ISF-H-BRS/ReDeX/Images/HubBack.jpg

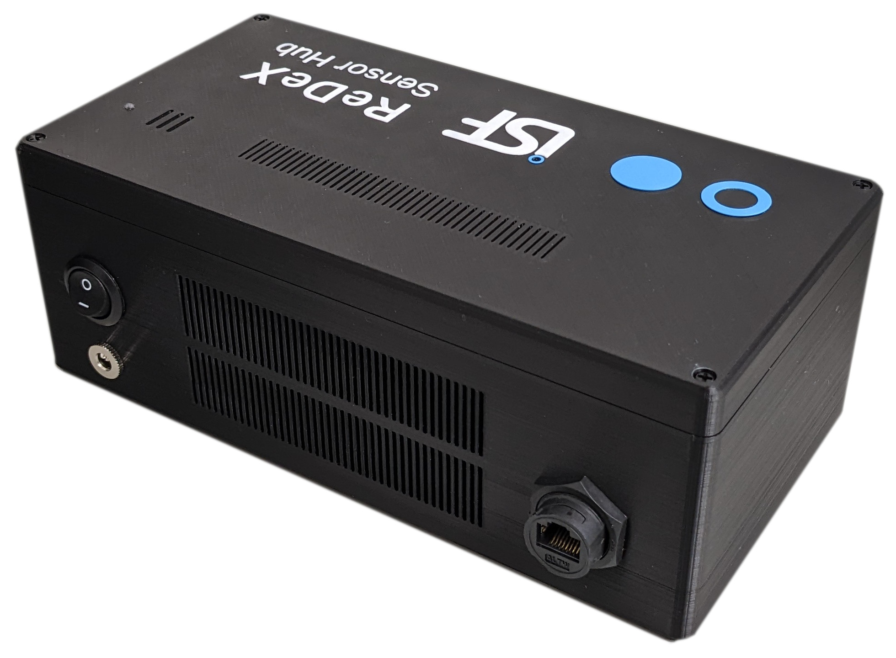
Images/HubBack.jpg
