ISF-H-BRS/ReDeX/Images/SensorViewer.png

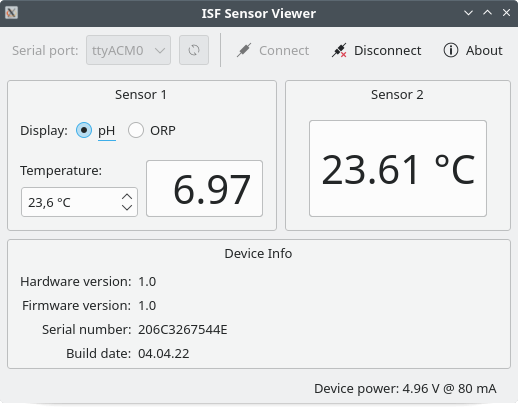
Images/SensorViewer.png
