ISF-H-BRS/ReDeX/Firmware/ConductanceMaster/Core/Inc/main.h

#define BUS_VOLTAGE_Pin GPIO_PIN_0
#define BUS_VOLTAGE_GPIO_Port GPIOA
#define BUS_CURRENT_Pin GPIO_PIN_1
#define BUS_CURRENT_GPIO_Port GPIOA
#define SLAVE2_CS_Pin GPIO_PIN_4
#define SLAVE2_CS_GPIO_Port GPIOA
#define SLAVE2_SCK_Pin GPIO_PIN_5
#define SLAVE2_SCK_GPIO_Port GPIOA
#define SLAVE2_MISO_Pin GPIO_PIN_6
#define SLAVE2_MISO_GPIO_Port GPIOA
#define SLAVE2_MOSI_Pin GPIO_PIN_7
#define SLAVE2_MOSI_GPIO_Port GPIOA
#define SLAVE2_CON_Pin GPIO_PIN_4
#define SLAVE2_CON_GPIO_Port GPIOC
#define SLAVE2_DRDY_Pin GPIO_PIN_5
#define SLAVE2_DRDY_GPIO_Port GPIOC
#define SLAVE1_CS_Pin GPIO_PIN_12
#define SLAVE1_CS_GPIO_Port GPIOB
#define SLAVE1_SCK_Pin GPIO_PIN_13
#define SLAVE1_SCK_GPIO_Port GPIOB
#define SLAVE1_MISO_Pin GPIO_PIN_14
#define SLAVE1_MISO_GPIO_Port GPIOB
#define SLAVE1_MOSI_Pin GPIO_PIN_15
#define SLAVE1_MOSI_GPIO_Port GPIOB
#define SLAVE1_CON_Pin GPIO_PIN_6
#define SLAVE1_CON_GPIO_Port GPIOC
#define SLAVE1_DRDY_Pin GPIO_PIN_7
#define SLAVE1_DRDY_GPIO_Port GPIOC
#define VARIANT1_Pin GPIO_PIN_11
#define VARIANT1_GPIO_Port GPIOC
#define VARIANT0_Pin GPIO_PIN_12
#define VARIANT0_GPIO_Port GPIOC
#define STATUS_BAD_Pin GPIO_PIN_3
#define STATUS_BAD_GPIO_Port GPIOB
#define STATUS_GOOD_Pin GPIO_PIN_4
#define STATUS_GOOD_GPIO_Port GPIOB
