ISF-H-BRS/ReDeX/Firmware/SensorBoard/Core/Src/User/sensormanager.cpp

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
#include "assert.h"
#include "config.h"
#include "sensormanager.h"

// ---------------------------------------------------------------------------------------------- //

SensorManager::SensorManager()
{
    static constexpr std::array<I2C_HandleTypeDef*, SensorCount> SensorHandles = {
        Config::Sensor1Handle, Config::Sensor2Handle
    };

    for (size_t i = 0; i < SensorCount; ++i)
    {
        ASSERT(m_sensors[i] == nullptr);

        char* buffer = m_memPool.getNextFreeBuffer();
        I2C_HandleTypeDef* handle = SensorHandles[i];

        const Sensor::Type type = readSensorType(i);

        switch (type)
        {
        case Sensor::Type::pH_ORP:
            m_sensors[i] = new (buffer) PhSensor(handle);
            break;

        case Sensor::Type::Temperature:
            m_sensors[i] = new (buffer) TemperatureSensor(handle);
            break;

        default:
            m_sensors[i] = new (buffer) NoneSensor();
            break;
        }
    }
}

// ---------------------------------------------------------------------------------------------- //

SensorManager::~SensorManager()
{
    for (auto& sensor : m_sensors)
    {
        if (sensor)
            sensor->~Sensor();

        sensor = nullptr;
    }
}

// ---------------------------------------------------------------------------------------------- //

auto SensorManager::sensorType(uint8_t sensor) const -> Sensor::Type
{
    ASSERT(sensor < SensorCount);
    return m_sensors[sensor]->type();
}

// ---------------------------------------------------------------------------------------------- //

auto SensorManager::sensorValue(uint8_t sensor) const -> double
{
    ASSERT(sensor < SensorCount);
    return m_sensors[sensor]->value();
}

// ---------------------------------------------------------------------------------------------- //

void SensorManager::update()
{
    for (auto sensor : m_sensors)
        sensor->update();
}

// ---------------------------------------------------------------------------------------------- //

auto SensorManager::readSensorType(uint8_t sensor) const -> Sensor::Type
{
    ASSERT(sensor < SensorCount);

    struct Input
    {
        GPIO_TypeDef* port;
        uint32_t pin;
    };

    static constexpr std::array<std::array<Input, 2>, SensorCount> Inputs = {{
        {{{ ID1_0_GPIO_Port, ID1_0_Pin }, { ID1_1_GPIO_Port, ID1_1_Pin }}},
        {{{ ID2_0_GPIO_Port, ID2_0_Pin }, { ID2_1_GPIO_Port, ID2_1_Pin }}}
    }};

    const Input& input0 = Inputs[sensor][0];
    const Input& input1 = Inputs[sensor][1];

    const GPIO_PinState state0 = HAL_GPIO_ReadPin(input0.port, input0.pin);
    const GPIO_PinState state1 = HAL_GPIO_ReadPin(input1.port, input1.pin);

    const unsigned int type = ((state1 == GPIO_PIN_SET ? 1 : 0) << 1) |
                              ((state0 == GPIO_PIN_SET ? 1 : 0) << 0);

    return static_cast<Sensor::Type>(type);
}

// ---------------------------------------------------------------------------------------------- //
