ISF-H-BRS/ReDeX/Firmware/Potentiostat/Core/Inc/main.h

#define PWR_ENABLE_Pin GPIO_PIN_14
#define PWR_ENABLE_GPIO_Port GPIOC
#define ADC_CONVST_Pin GPIO_PIN_2
#define ADC_CONVST_GPIO_Port GPIOA
#define ADC_CS1_Pin GPIO_PIN_3
#define ADC_CS1_GPIO_Port GPIOA
#define ADC_CS2_Pin GPIO_PIN_4
#define ADC_CS2_GPIO_Port GPIOA
#define ADC_SCK_Pin GPIO_PIN_5
#define ADC_SCK_GPIO_Port GPIOA
#define ADC_MISO_Pin GPIO_PIN_6
#define ADC_MISO_GPIO_Port GPIOA
#define DAC_AUX_Pin GPIO_PIN_7
#define DAC_AUX_GPIO_Port GPIOA
#define STATUS_GOOD_Pin GPIO_PIN_0
#define STATUS_GOOD_GPIO_Port GPIOB
#define STATUS_BAD_Pin GPIO_PIN_1
#define STATUS_BAD_GPIO_Port GPIOB
#define OUTPUT_ENABLE_Pin GPIO_PIN_8
#define OUTPUT_ENABLE_GPIO_Port GPIOA
#define MUX_A0_Pin GPIO_PIN_3
#define MUX_A0_GPIO_Port GPIOB
#define MUX_A1_Pin GPIO_PIN_4
#define MUX_A1_GPIO_Port GPIOB
#define MUX_EN_Pin GPIO_PIN_5
#define MUX_EN_GPIO_Port GPIOB
#define SCL_Pin GPIO_PIN_6
#define SCL_GPIO_Port GPIOB
#define SDA_Pin GPIO_PIN_7
#define SDA_GPIO_Port GPIOB
