ISF-H-BRS/ReDeX/Firmware/ConductanceSlave/Core/Src/User/signalgenerator.cpp

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
#include "signalgenerator.h"
#include "wavegenerator.h"

#include <algorithm> // for clamp()

// ---------------------------------------------------------------------------------------------- //

namespace {
    constexpr uint32_t DacZeroChannel   = DAC_CHANNEL_1;
    constexpr uint32_t DacSignalChannel = DAC_CHANNEL_2;
    constexpr uint32_t DacDcOffset      = 2047;
    constexpr uint32_t DacMaximumValue  = 4095;
}

// ---------------------------------------------------------------------------------------------- //

SignalGenerator::SignalGenerator()
{
    HAL_DAC_Start(m_dacHandle, DacZeroChannel);
    HAL_DAC_Start(m_dacHandle, DacSignalChannel);

    setValue(DacZeroChannel, DacDcOffset);
    setValue(DacSignalChannel, DacDcOffset);
}

// ---------------------------------------------------------------------------------------------- //

SignalGenerator::~SignalGenerator()
{
    HAL_DAC_Stop(m_dacHandle, DacZeroChannel);
    HAL_DAC_Stop(m_dacHandle, DacSignalChannel);
}

// ---------------------------------------------------------------------------------------------- //

void SignalGenerator::reset()
{
    m_waveform = Waveform::None;
    m_frequency = 1.0;
    m_amplitude = 0.0;

    m_signalPosition = 0;

    setValue(DacSignalChannel, DacDcOffset);
}

// ---------------------------------------------------------------------------------------------- //

void SignalGenerator::setup(Waveform waveform, unsigned int frequency, Real amplitude)
{
    frequency = std::clamp(frequency, MinimumFrequency, MaximumFrequency);
    amplitude = std::clamp(amplitude, MinimumAmplitude, MaximumAmplitude);

    m_waveform = waveform;
    m_frequency = static_cast<Real>(frequency);
    m_amplitude = 0.5 / MaximumAmplitude * amplitude;
}

// ---------------------------------------------------------------------------------------------- //

void SignalGenerator::update()
{
    using WaveGenerator = WaveGenerator<Real>;

    static constexpr auto DcOffset = static_cast<Real>(0.5);
    static constexpr auto One = static_cast<Real>(1.0);
    static constexpr auto Zero = static_cast<Real>(0.0);

    const Real time = m_signalPosition * (One / SampleRate);

    if (++m_signalPosition >= SampleRate)
        m_signalPosition = 0;

    Real signal = DcOffset;

    if (m_waveform == Waveform::Sine)
        signal = WaveGenerator::qsine(time, m_frequency, m_amplitude, DcOffset);
    else if (m_waveform == Waveform::Square)
        signal = WaveGenerator::square(time, m_frequency, m_amplitude, DcOffset);
    else if (m_waveform == Waveform::Triangle)
        signal = WaveGenerator::triangle(time, m_frequency, m_amplitude, DcOffset);
    else if (m_waveform == Waveform::Sawtooth)
        signal = WaveGenerator::sawtooth(time, m_frequency, m_amplitude, DcOffset);

    signal = std::clamp(signal, Zero, One);

    const uint16_t outValue = static_cast<uint16_t>(DacMaximumValue * signal);
    setValue(DacSignalChannel, outValue);
}

// ---------------------------------------------------------------------------------------------- //

void SignalGenerator::setValue(uint32_t channel, uint32_t value)
{
    HAL_DAC_SetValue(m_dacHandle, channel, DAC_ALIGN_12B_R, value);
}

// ---------------------------------------------------------------------------------------------- //
