ISF-H-BRS/ReDeX/Firmware/Potentiostat/Core/Inc/User/ltc2945.h

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
#pragma once

#include <cstdint>
#include <span>

class Ltc2945
{
public:
    enum class Address : uint8_t
    {
        A0 = 0xce,
        A1 = 0xd0,
        A2 = 0xd2,
        A3 = 0xd4,
        A4 = 0xd6,
        A5 = 0xd8,
        A6 = 0xda,
        A7 = 0xdc,
        A8 = 0xde
    };

    static constexpr uint8_t AddressCount = 9;

    class Interface
    {
        friend class Ltc2945;

        virtual void write(uint8_t address, uint8_t reg, std::span<const uint8_t> data) = 0;
        virtual void read(uint8_t address, uint8_t reg, std::span<uint8_t> data) = 0;
    };

public:
    Ltc2945(Interface* interface, Address address, float resistance);

    void reset();

    void setEnabled(bool enable);
    auto isEnabled() const -> bool;

    void setVoltageLimits(float lower, float upper);
    void setCurrentLimits(float lower, float upper);
    void setPowerLimits(float lower, float upper);

    auto getVoltage() const -> float;
    auto getCurrent() const -> float;
    auto getPower() const -> float;

private:
    void writeRegister(uint8_t reg, std::span<const uint8_t> buffer);
    void readRegister(uint8_t reg, std::span<uint8_t> buffer) const;

    void writeRegister8(uint8_t reg, uint8_t data);
    auto readRegister8(uint8_t reg) const -> uint8_t;

    void writeRegister12(uint8_t reg, uint16_t data);
    auto readRegister12(uint8_t reg) const -> uint16_t;

    void writeRegister24(uint8_t reg, uint32_t data);
    auto readRegister24(uint8_t reg) const -> uint32_t;

    auto voltageToValue(float voltage) const -> uint16_t;
    auto valueToVoltage(uint16_t value) const -> float;

    auto currentToValue(float current) const -> uint16_t;
    auto valueToCurrent(uint16_t value) const -> float;

    auto powerToValue(float power) const -> uint32_t;
    auto valueToPower(uint32_t value) const -> float;

private:
    Interface* m_interface;
    const uint8_t m_address;
    const float m_resistance;
};
