ISF-H-BRS/ReDeX/Software/TcpServer/devicemanager.h

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
#pragma once

#include "configuration.h"
#include "macro.h"
#include "testpoint.h"

#include <map>
#include <memory>

class DeviceManager
{
    REDEX_DELETE_COPY_MOVE(DeviceManager);

public:
    explicit DeviceManager(const Configuration& config);
    ~DeviceManager();

    auto nodes() const -> const std::vector<Node*>&;
    auto sensors() const -> const std::vector<Sensor*>&;
    auto testpoints() const -> const std::vector<Testpoint*>&;

    auto findNode(const QString& id) const -> Node*;
    auto findSensor(const QString& id) const -> Sensor*;
    auto findTestpoint(const QString& id) const -> Testpoint*;

private:
    template <typename T>
    auto getNode(const QString& id) const -> T*;

    template <typename T>
    auto getSensor(const QString& id) const -> T*;

    auto makeConductanceSensor(const Configuration::Sensor& sensor) const -> SensorPtr;
    auto makePotentiostatSensor(const Configuration::Sensor& sensor) const -> SensorPtr;
    auto makeSensorsSensor(const Configuration::Sensor& sensor) const -> SensorPtr;

    auto makeNode(const Configuration::Node& node) const -> NodePtr;
    auto makeSensor(const Configuration::Sensor& sensor) const -> SensorPtr;
    auto makeTestpoint(const Configuration::Testpoint& testpoint) const -> TestpointPtr;

    static auto getId(const QString& id) -> QString;
    static auto getInt(const QString& value) -> int;
    static auto getUInt(const QString& value) -> unsigned int;
    static auto getDouble(const QString& value) -> double;
    static auto getBool(const QString& value) -> bool;

private:
    std::map<QString,NodePtr> m_nodeMap;
    std::map<QString,SensorPtr> m_sensorMap;
    std::map<QString,TestpointPtr> m_testpointMap;

    std::vector<Node*> m_nodes;
    std::vector<Sensor*> m_sensors;
    std::vector<Testpoint*> m_testpoints;
};
